William-Souza-Santos/DIGITAL_PID_CONTROL_DCDC_CONVERTER/04 - Text/MATLAB_4SBBC_2.pdf

### 1. Configuração básica de um conversor Buck-Boost

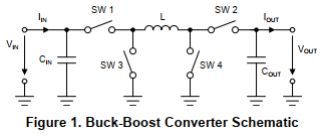
[picture p117: figure]

### 2. Princípio de operação

D̅ = 1 − D

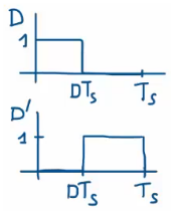
[picture p118: figure]

### 2.1 Buck síncrono

D =

Vo
Vi

Vi > Vo
Apenas duas chaves são comutadas;
Não é possível operar com Vi = Vo or D = 1;
Q3 é totalmente ligado e Q4 é totalmente desligado. Q1 e Q2 são controlados por D e 1 - D, respectivamente, e o conversor se torna um conversor buck sincronizado, conforme mostrado na Figura 4.


### 2.2 Boost síncrono

D = 1 −

Vi
Vo
Apenas duas chaves são comutadas;
Não é possível operar com Vi = Vo or D = 0.
Q1 é totalmente ligado e Q2 é totalmente desligado. Q4 e Q3 são controlados por D e 1 - D, respectivamente, e o conversor se torna um conversor boost sincronizado, conforme mostrado na Figura 5.

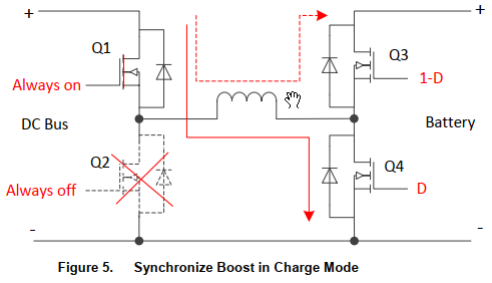
[picture p119: figure]

### 2.3 Buck-Boost síncrono

D =

Vo
Vi + Vo

Vi ≈ Vo
Four switches commutate;
Não é possível operar com Vi = Vo or D = 0.5; Maiores perdas de comutação;
Menor eficiência;
Q1 e Q4 são controlados por D, Q2 e Q3 são controlados por 1-D. O conversor se torna um conversor buck-boost sincronizado, conforme mostrado na Figura 6.

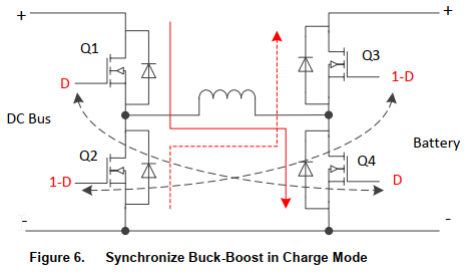
[picture p120: figure]

### 3. Modo de operação

Os quatro interruptores alteram o modo de operação de acordo com a tensão de entrada e a tensão de saída, conforme mostrado na Figura 10. Para evitar um salto entre as operações, uma histerese é adicionada entre a transição do modo buck e buck-boost e entre o modo buck-boost e boost.

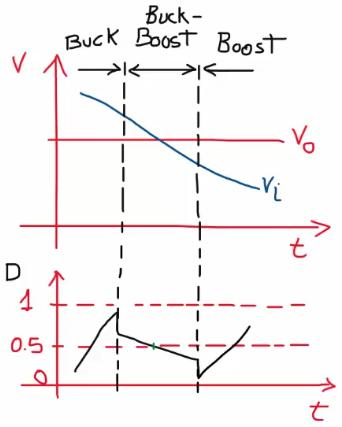
[picture p121: figure]
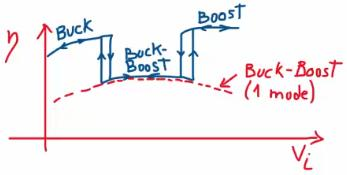
[picture p122: figure]

Um compensador deve ser projetado para operação estável; Há perturbações transitórias durante mudanças de modo.

### 4. Implementação

MOSFETs usados como interruptores;
Os switches superiores (S1, S3) precisam ser acionados;
O tempo de inatividade deve ser adicionado para evitar a corrente de disparo;

Um Bootstrap não pode ser usado: ele não consegue manter os interruptores do lado alto continuamente ligados;
Soluções típicas: gate drivers baseados em transformador e gate drivers baseados em optoacoplador.

### 4.1 Buck

D =

Vo
Vi

L =

1
fΔiL

∗ (Vo −
Vo

2
Vi

)

C =

ΔiL
8fΔVo

### 4.2 Buck-Boost

D =

Vo
Vo + Vi

L =

1
fΔiL

∗

Vo

1 +

Vo
Vi

C =

Io
fΔVo

∗

Vo
Vo + Vi

### 4.3 Boost

D =

Vo − Vi
Vo

L =

1
fΔiL

∗ (Vi −
Vi

2
Vo

)

C =

Io
fΔVo

∗

Vo − Vi
Vo

### 5. Design example

Faixa de tensão de entrada: Vi = [18,30] V Faixa de ciclo de trabalho: D = [0.2,0.8]

Modo de operação | Ciclo de trabalho
Buck | D =
| 1 Vi Vo
Buck-boost | D =
| 1
| 1 + Vi Vo
Boost | D = 1 − Vi Vo

### 5.1 Região Buck

Primeiro calculamos os valores mínimos e máximos da tensão de saída possíveis nessa região com base no ciclo de trabalho determinado.

0.2 =

1
30

Vomin

→ Vomin = 6 V

0.8 =

1
30

Vomax

→ Vomax = 24 V

Agora calculamos uma relação entrada e saída que limitam essa região.

30
24 <

Vi
Vo

≤

30
6

1.25 <

Vi
Vo

≤ 5

Com o limite esquerdo, calculamos as tensões de saída máximas com base na tensão de entrada que determinam a fronteira com a região Buck-Boost.

1.25 =

18
Vo1

→ Vo1 = 14.4 V

1.25 =

30
Vo2

→ Vo2 = 24 V

### 5.2 Região Boost

Primeiro calculamos os valores mínimos e máximos da tensão de saída possíveis nessa região com base no ciclo de trabalho determinado.

0.2 = 1 −

18

Vomin

→ Vomin = 22.5 V

0.8 = 1 −

30

Vomax

→ Vomax = 150 V

Agora calculamos uma relação entrada e saída que limitam essa região.

30
150 ≤

Vi
Vo

<

18
22.5

0.2 ≤

Vi
Vo

< 0.8

Com o limite direito, calculamos as tensões de saída mínimas com base na tensão de entrada que determinam a fronteira com a região Buck-Boost.

18
Vo1

= 0.8 → Vo1 = 22.5 V

30
Vo2

= 0.8 → Vo2 = 37.5 V

### 5.3 Regiões de operação

Faixa de tensão de saída: Vo = [6,55] V

Modo de operação | Ciclo de trabalho | Região de operação | Tensão de operação
Buck | D =
| 1 Vi Vo | Vi Vo > 1.25 | Vi = [18,30] Vo = [6,24]
Buck-Boost | D =
| 1 1 + Vi Vo | 0.80 ≤ Vi Vo ≤ 1.25 | Vi = [18,30] Vo = [14.4,37.5]
Boost | D = 1 − Vi Vo | Vi Vo
| | < 0.80 | Vi = [18,30] Vo = [22.5,55]

### 5.3.1 Regiões de operação


RegionPlot[
{y/x>1.25,0.8<=y/x<=1.25,y/x<0.8}, {x,6,55},
{y,18,30},
PlotStyle->{Blue,Yellow,Red},
BoundaryStyle->None,
FrameLabel->{"Tensão de Saída","Tensão de Entrada"}, PlotLabel->"Região de Operação",
PlotLegends->{"Buck","Buck-Boost","Boost"}]

Com as regiões limitadas, podemos determinar o valor mínimo e máximo da região de operação, conforme a seguir.

0.2 ≤

Vi
Vo

< 0.8 ∩ 1.25 <

Vi
Vo

≤ 5

0.2 ≤

Vi
Vo

≤ 5

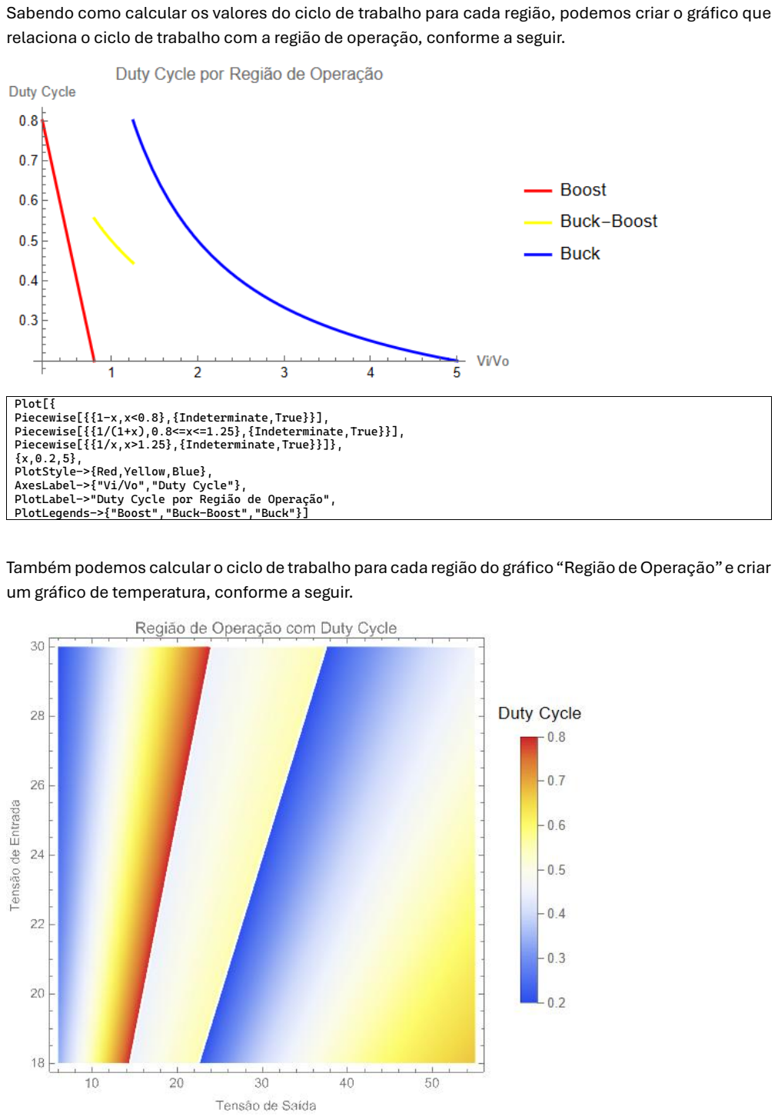
[picture p123: page 10]

Sabendo como calcular os valores do ciclo de trabalho para cada região, podemos criar o gráfico que relaciona o ciclo de trabalho com a região de operação, conforme a seguir.

Plot[{
Piecewise[{{1-x,x<0.8},{Indeterminate,True}}], Piecewise[{{1/(1+x),0.8<=x<=1.25},{Indeterminate,True}}], Piecewise[{{1/x,x>1.25},{Indeterminate,True}}]}, {x,0.2,5},
PlotStyle->{Red,Yellow,Blue},
AxesLabel->{"Vi/Vo","Duty Cycle"}, PlotLabel->"Duty Cycle por Região de Operação",
PlotLegends->{"Boost","Buck-Boost","Buck"}]

Também podemos calcular o ciclo de trabalho para cada região do gráfico “Região de Operação” e criar um gráfico de temperatura, conforme a seguir.

DensityPlot[
Piecewise[{
{x/y,y/x>1.25},
{x/(x+y),0.8<=y/x<=1.25},
{(x-y)/x,y/x<0.8}}],
{x,6,55},
{y,18,30},
ColorFunction->"TemperatureMap", PlotLegends->BarLegend[{"TemperatureMap",{0.2,0.80}}, LegendLabel->"Duty Cycle",
Ticks->Range[0,1,0.1]],
FrameLabel->{"Tensão de Saída","Tensão de Entrada"}, PlotLabel->"Região de Operação com Duty Cycle", RegionFunction->Function[{x,y},6<=x<=55&&18<=y<=30], PlotPoints->64]
Plot3D[
Piecewise[{
{x/y,y/x>1.25},
{x/(x+y),0.80<=y/x<=1.25},
{(x-y)/x,y/x<0.8}}],
{x,6,55},{y,18,30},
AxesLabel->{"Tensão de Saída","Tensão de Entrada","Duty Cycle"}, ColorFunction->Function[{x,y,z},If[y/x>1.25,Blue,If[0.80<=y/x<=1.25,Yellow,Red]]],ColorFunctionScaling->False,BoxRatios->{1,1,1}]

### 5.4 Cálculo dos componentes

Output current: Io = 2 A
Switching frequency: f = 10 kHz Inductor current ripple: 0.6 A (30%)
Output voltage ripple: 1 V (2%)
Modo de operação | Tensão de operação
Buck | Vi = [18,30]
| Vo = [6,24]
Buck-Boost | Vi = [18,30]
| Vo = [14.4,37.5]
Boost | Vi = [18,30]
| Vo = [22.5,55]

### 5.4.1 Buck

Lmax =

1
fΔiL

∗ (Vo −
Vo

2

Vimax

) =
1
10 ∗ 10³ ∗ 0.6

∗ (Vo −
Vo

2
30)

d
dVo

Lmax = 0 → Vo = 15 V

Lmax =

1
10 ∗ 10³ ∗ 0.6

∗ (15 −

15²
30 ) = 1.25 mH

Io=2;
f=10*10^3;
Lr=0.6;
Vr=1;
Lmax[Vi_,Vo_]:=1/(f*Lr)(Vo-Vo^2/Vi); NMaximize[{Lmax[Vi,Vo],18<=Vi<=30,6<=Vo<=24},{Vi,Vo}]
C =

ΔiL
8fΔVo

=

0.6
8 ∗ 10 ∗ 10³ ∗ 1

= 7.5 uF

### 5.2 Buck-Boost

Lmax =

1
fΔiL

∗

Vomax

1 +

Vomax
Vimax

=

1
10 ∗ 10³ ∗ 0.6

∗

37.5

1 +

37.5
30

= 2.78 mH

Cmax =

Io
fΔVo

∗

Vomax

Vomax + Vimin

=

2
10 ∗ 10³ ∗ 1

∗

37.5
37.5 + 18 = 135.1 uF

### 5.3 Boost

Lmax =

1
fΔiL

∗ (Vi −
Vi

2

Vomax

) =
1
10 ∗ 10³ ∗ 0.6

∗ (Vi −
Vi

2
55)

d
dVi

Lmax = 0 → Vi = 27.5 V

Lmax =

1
10 ∗ 10³ ∗ 0.6

∗ (27.5 −
27.5

2
55 ) = 2.29 mH

Io=2;
f=10*10^3;
Lr=0.6;
Vr=1;
Lmax[Vi_,Vo_]:=1/(f*Lr)*(Vi-Vi^2/Vo); NMaximize[{Lmax[Vi,Vo],18<=Vi<=30,22.5<=Vo<=55},{Vi,Vo}]

Cmax =

Io
fΔVo

∗

Vomax − Vimin

Vomax

=

2
10 ∗ 10³ ∗ 1

∗

55 − 18
55 = 134.5 uF

### 5.4 Verification

L = 2.78 mH

C = 135.1 uF

### 5.4.1 Buck

2.78 ∗ 10⁻³ =

1
10 ∗ 10³ ∗ ΔiL

∗ (15 −

15²
30 ) → ΔiL = 0.27 A

135.1 ∗ 10⁻⁶ =

0.27
8 ∗ 10 ∗ 10³ ∗ ΔVo

→ ΔVo = 0.025 V

### 5.4.2 Buck-Boost

2.78 ∗ 10⁻³ =

1
10 ∗ 10³ ∗ ΔiL

∗

37.5

1 +

37.5
30

→ ΔiL = 0.6 A

135.1 ∗ 10⁻⁶ =

2
10 ∗ 10³ ∗ ΔVo

∗

37.5
37.5 + 18

→ ΔVo = 1 V

### 5.4.2 Boost

2.78 ∗ 10⁻³ =

1
10 ∗ 10³ ∗ ΔiL

∗ (27.5 −
27.5

2
55 ) → ΔiL = 0.49 A

135.1 ∗ 10⁻⁶ =

2
10 ∗ 10³ ∗ ΔVo

∗

55 − 18
55

→ ΔVo = 1 V

Modo de
operação

Faixa de
operação (V) | Duty Cycle | Vi/Vo | ΔiLmax
| | | (A)

ΔVomax
(V)
Buck | Vi = [18,30]
Vo = [6,24] | D = [0.2,0.8] | 0.2 ≤ Vi
| | Vo
< 0.8 | 0.27 | 0.025

Buck-Boost

Vi = [18,30] Vo = [14.4,37.5] | D = [0. 4̅, 0. 5̅] | 0.8 ≤ Vi
| | Vo
≤ 1.25 | 0.6 | 1
Boost | Vi = [18,30]
Vo = [22.5,55] | D = [0.2,0.8] | 1.25 < Vi
| | Vo
≤ 5 | 0.49 | 1

### 5.5 Simulink implementation

O circuito base do conversor é implementado no Simulink em um subsistema conforme abaixo.

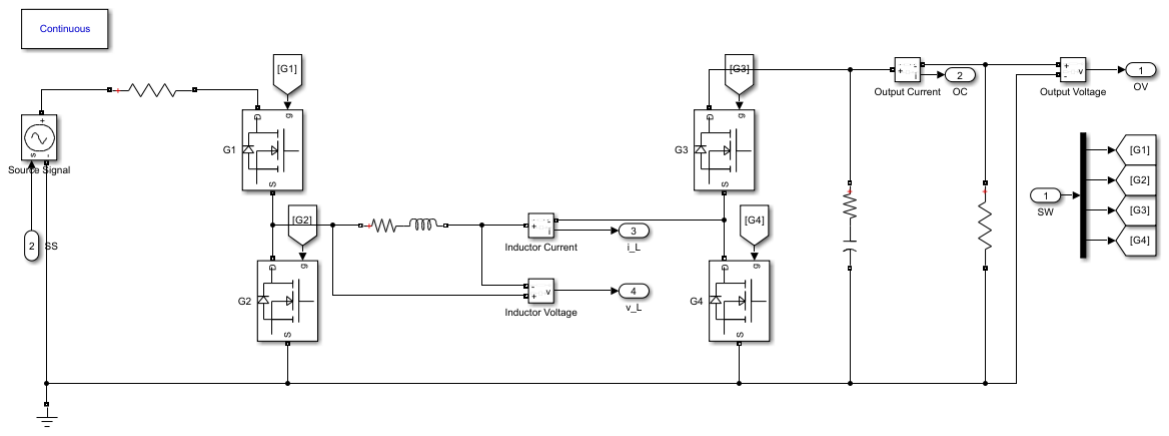
[picture p124: figure]

O subsistema possui 2 entradas, sendo elas: Source Signal (SS) e SW ( 4 Switches multiplexados). E 4 saídas, sendo elas: Output Voltage (OV), Output Current (OC), Inductor Voltage (v_L) e Inductor Current (i_L).
Os 4 modos de funcionamento dependem do estado dos 4 Switches e do seu Duty Cycle respectivo. Como temos 4 modos diferentes, precisamos de 2 bits para representar os modos. A tabela abaixo resume a lógica da ativação de cada Switch usando A e B como entradas lógicas.
Mode | AB | SW1 | SW2 | SW3 | SW4
Buck | 00 | D | 1 - D | 1 | 0
Buck-boost | 01 | D | 1 - D | 1 - D | D
Boost | 11 | 1 | 0 | 1 - D | D
Off | 10 | 0 | 0 | 0 | 0

Usando conhecimentos de sistemas digitais, podemos simplificar a relação para cada Switch, chegando nas equações abaixo.

SW1 = A̅D + AB

SW2 = A̅D̅

SW3 = A̅B̅ + BD̅

SW4 = BD

A partir das relações acima, podemos implementar no Simulink um subsistema para aplicar o funcionamento de cada Switch a partir das entradas A, B e D.


O modo de funcionamento atual e futuro do sistema é definido a partir da relação entre Tensão de Entrada e Tensão de Referência, conforme a tabela abaixo.

Modo de operação | Vi/Vo
Buck | 1.25 <

Vi
Vo

≤ 5

Buck-Boost 0.8 ≤

Vi
Vo

≤ 1.25

Boost | 0.2 ≤

Vi
Vo

< 0.8

A tabela indica que, enquanto a Tensão de Entrada estiver acima de 125% da Tensão de Referência, o modo de funcionamento será Buck. E, enquanto a Tensão de Entrada estiver abaixo de 80% da Tensão de Referência, o modo de funcionamento será Boost.
Podemos escrever essa relação conforme abaixo.

X =

Vi
Vo

> 1.25

Y =

Vi
Vo

> 0.8

A tabela abaixo resume a lógica do modo de funcionamento acima.

XY | Buck | Buck-Boost | Boost
00 | 0 | 0 | 1
01 | 0 | 1 | 0
11 | 1 | 0 | 0
10 | X | X | X

Usando conhecimentos de sistemas digitais, podemos simplificar a relação, chegando nas equações abaixo.

Buck = X

Buck-Boost = X̅Y

Boost = Y̅
A lógica acima pode ser implementada no Simulink usando o subsistema a seguir.

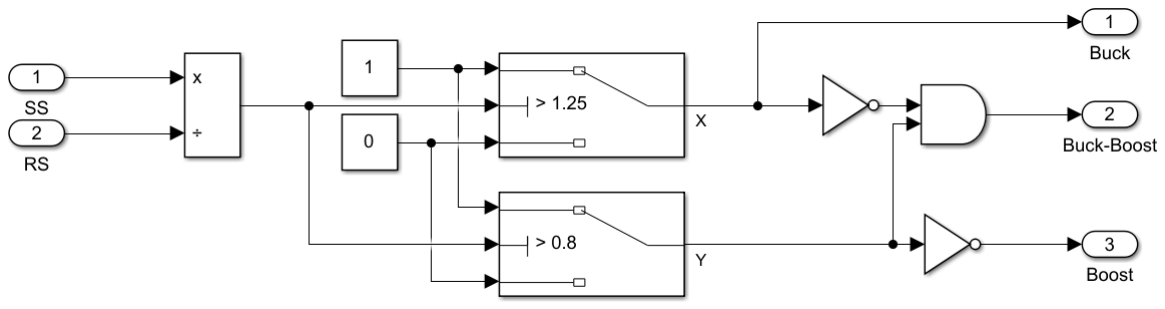
[picture p125: figure]

Agora que temos definido qual modo será ativado, precisamos do cálculo do Duty Cycle. Cada modo terá seu Duty Cycle calculado, porém somente aquele ativado no momento será usado no funcionamento dos Switches. Conforme vimos anteriormente, para o cálculo precisamos somente da Tensão de Entrada e Tensão de Referência, conforme a seguir.


O valor de A e B, escolhido anteriormente conforme a tabela abaixo, também é anexado junto ao seu respectivo D pelo MUX.

Mode | AB
Buck | 00
Buck-boost | 01
Boost | 11

Para definir qual valor será utilizado, usamos o resultado do subsistema anterior juntamente com comparadores lógicos para levar o valor até as variáveis A, B e D pelo DEMUX, conforme abaixo.

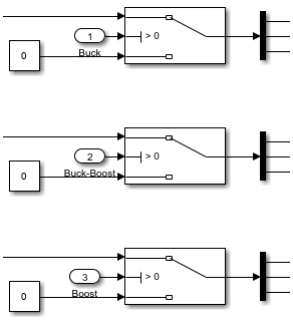
[picture p126: figure]

Como somente um dos comparadores estará ativo por vez, A e B pode ser calculado com uma porta OR enquanto D pode ser calculado como uma soma simples, conforme abaixo.

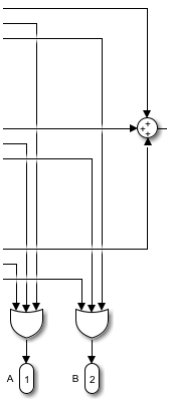
[picture p127: figure]

Por fim, para propósitos de controle, podemos somar a variável D com uma entrada externa (D_FIS). Também, como definido anteriormente, o Duty Cycle é saturado entre 0.2 e 0.8.

Assim, obtemos nosso subsistema responsável por determinar a variável D do sistema.


Com as variáveis A, B e D determinadas, o funcionamento dos Switches também estão determinados e, portanto, o sistema está pronto para funcionamento em malha aberta.
Para visualizar o erro e sua variação precisamos de um subsistema. O erro pode ser definido pelo quão distante está a Tensão de Saída da Tensão de Referência e a variação do erro pode ser definida pela diferença entre o erro atual e anterior, assumindo o uso de valores discretos. Para facilitar a visualização do desempenho, vamos empregar um erro normalizado, conforme abaixo.

E[n] =

Vo − Vr
|Vo − Vr

| + 1

dE[n] = E[n] − E[n − 1]

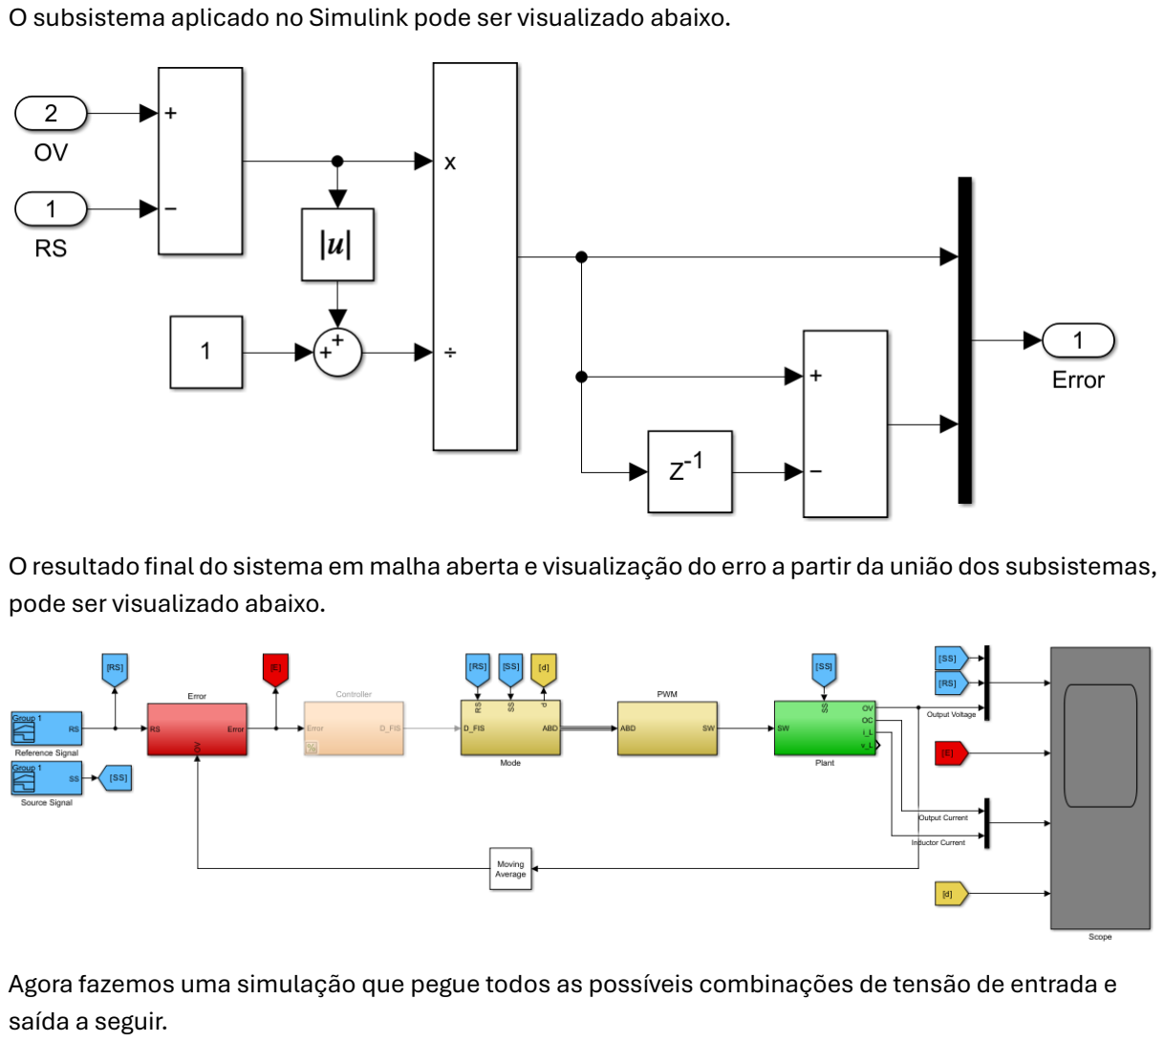
[picture p128: page 19]

O subsistema aplicado no Simulink pode ser visualizado abaixo.

O resultado final do sistema em malha aberta e visualização do erro a partir da união dos subsistemas, pode ser visualizado abaixo.

Agora fazemos uma simulação que pegue todos as possíveis combinações de tensão de entrada e saída a seguir.

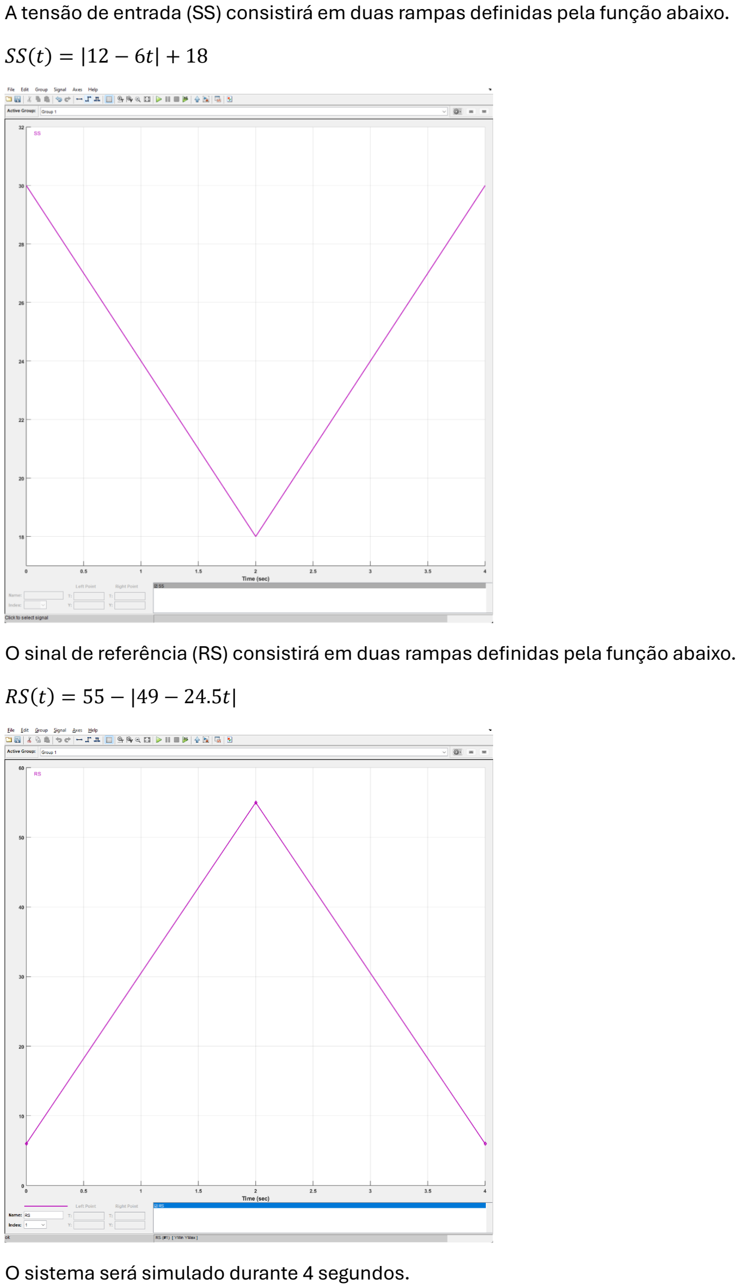
[picture p129: page 20]

A tensão de entrada (SS) consistirá em duas rampas definidas pela função abaixo.

SS(t) = |12 − 6t| + 18

O sinal de referência (RS) consistirá em duas rampas definidas pela função abaixo.

RS(t) = 55 − |49 − 24.5t|

O sistema será simulado durante 4 segundos.


Podemos identificar facilmente os pontos de transição do modo de operação pela falta de histerese. Também se observa um erro na tensão de saída (vermelho) pela falta de um compensador.


Nota-se uma taxa de variação inicial do erro (magenta) por causa da ativação do sistema até sua operação em estado estacionário, e outras variações durante a troca de operação. O erro (vermelho) indica que o sistema não atinge e fica abaixo da tensão de referência durante seu funcionamento pela falta de um compensador.

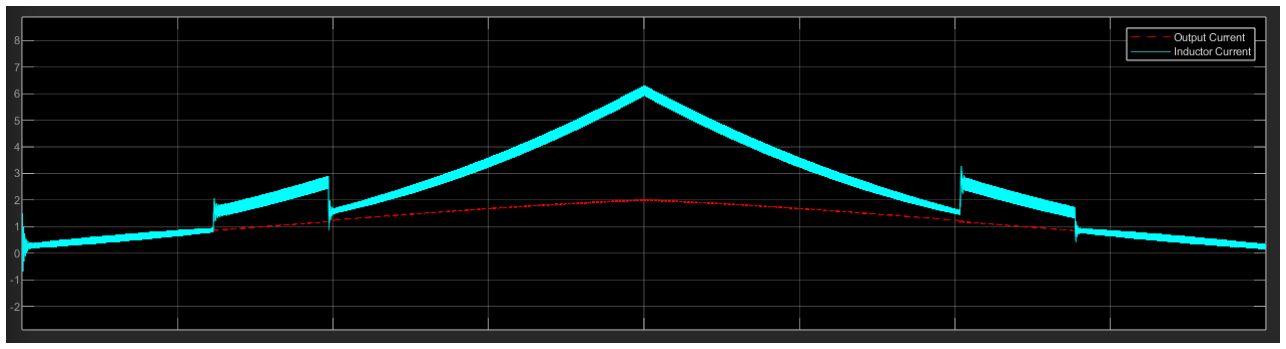
[picture p130: figure]

A corrente do indutor ficou abaixo de 6 A, não levando em consideração o ripple de 0.6 A. A corrente de saída permaneceu abaixo 2 A.


O valor do Duty Cycle obedece ao cálculo do modo de operação e se mantém no range designado anteriormente de 0.2 a 0.8. O valor do controle segue os mesmos valores pois não há um compensador implementado.

### 5.5.1 Controle

Usaremos um Fuzzy Inference System (FIS) como compensador e corrigir o erro do sistema. Sabemos que o comportamento do sistema depende do Duty Cycle, então iremos compensar esse valor e usá-la como variável manipulada.
A partir do subsistema de erro, temos que ele varia entre -1 e 1. Um erro negativo indica que a Tensão de Saída (variável controlada) está abaixo da Tensão de Referência e precisamos de uma compensação positiva no Duty Cycle, enquanto um erro positivo indica estar acima e precisamos de uma compensação negativa.
Com as informações anteriores, podemos criar um FIS com uma entrada, denominada Error, e uma saída, denominada Mode. Para determinar os pesos das entradas usaremos uma função membro em formato Z para erros negativos e uma função membro em formato S para erros positivos, conforme a abaixo.


Para determinar o ajuste na saída, usaremos uma função membro em formato de sino para saídas negativas e saídas positivas, conforme abaixo.


Com isso, obtemos uma superfície que descreve o comportamento do FIS.


Observando o gráfico acima, percebemos que erros próximos de 0 terão poucos ajustes, enquanto erros próximos de -0.5 e 0.5 terão seus ajustes máximos. Isso reflete o erro normalizado, que cresce muito quando se afaste de 0.

Agora criaremos uma tabela verdade que irá servir de consulta para determinar a saída com base na superfície anterior, a tabela verdade terá 32 pontos.


Com isso podemos criar o subsistema de controle que aplica a tabela verdade para compensar o Duty Cycle no sistema, conforme a seguir.

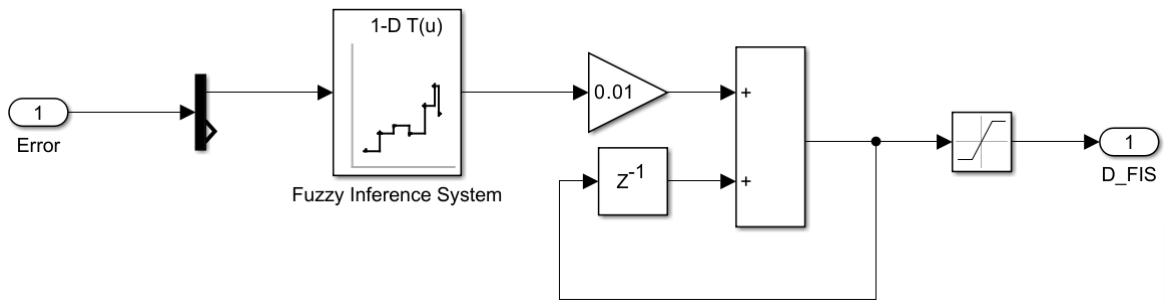
[picture p131: figure]

Para evitar ajustes instantâneos no sistema e instabilidade, adicionamos um integrador discreto que leva até o ponto de ajuste de forma suave. Também um saturador é utilizado para evitar acúmulo de esforço no integrador.

Por fim, temos o sistema completo no Simulink, conforme abaixo.

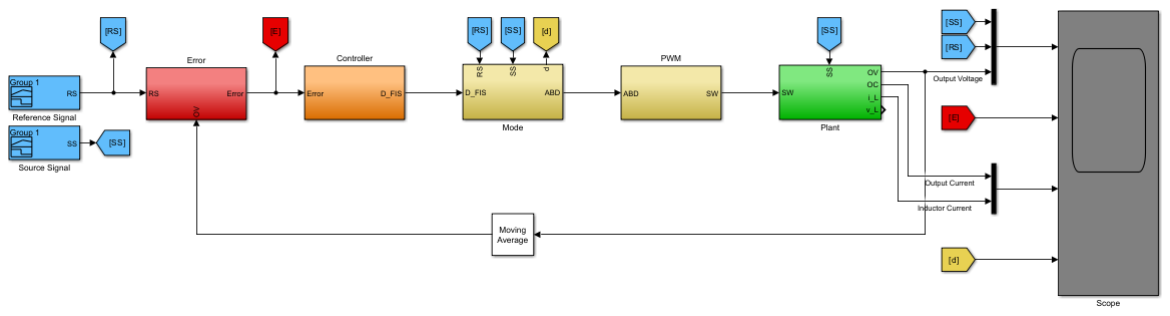
[picture p132: figure]

A simulação seguirá as mesmas condições anteriores, porém com a adição do controlador.


Podemos identificar facilmente os pontos de transição do modo de operação pela falta de histerese. Também se observa que a saída acompanhou a tensão de referência.

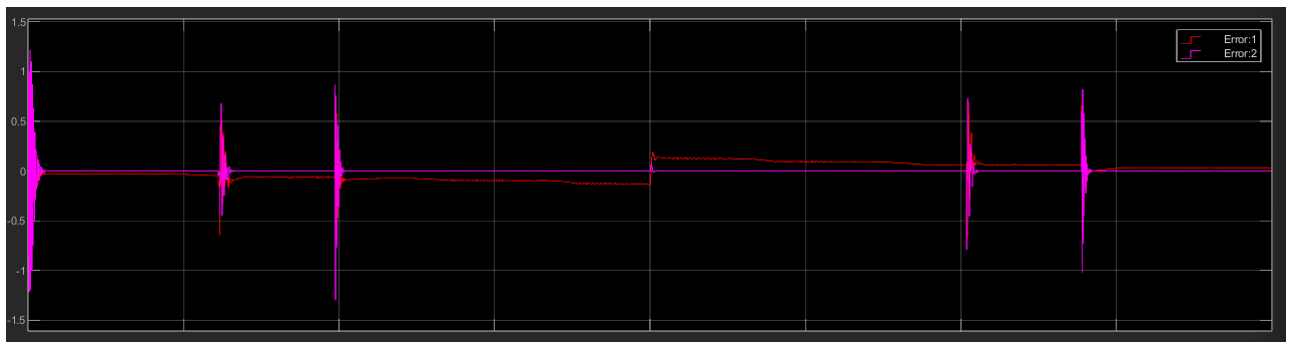
[picture p133: figure]

Nota-se uma taxa de variação inicial do erro (magenta) por causa da ativação do sistema até sua operação em estado estacionário, e outras variações durante a troca de operação. O erro (vermelho) indica que a saída do sistema fica próximo da tensão de referência, porém não exatamente 0, considerando o uso de um erro normalizado.

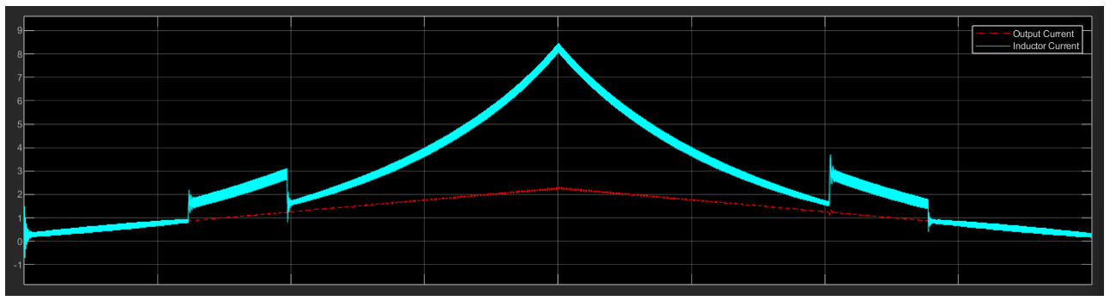
[picture p134: figure]

A corrente do indutor ficou abaixo de 8 A, não levando em consideração o ripple de 0.6 A. A corrente de saída permaneceu abaixo 2 A. Ou seja, pela ação do compensador houve um aumento na corrente de entrada.


O valor do Duty Cycle obedece ao cálculo do modo de operação e se mantém no range designado anteriormente de 0.2 a 0.8. O valor do controlado foi compensado, principalmente na parte com modo de operação Buck-Boost.
Com isso observamos que para realizar a correção houve um aumento na corrente de entrada, que deverá ser levado em conta no projeto.
