William-Souza-Santos/DIGITAL_PID_CONTROL_DCDC_CONVERTER/04 - Text/Fonte/buck_boost_formulas.pdf

## Dimensionamento de um Conversor DC-DC Buck-Boost Bidirecional

1. Razão Cíclica (Duty Cycle)
- Modo Buck (Step-Down):
D = V_out / V_in
Onde:
- D = razão cíclica
- V_out = tensão de saída
- V_in = tensão de entrada
- Modo Boost (Step-Up):
D = 1 - (V_in / V_out)
- Modo Buck-Boost:
D = V_out / (V_out + V_in)
2. Indutor
- Corrente Média no Indutor:
I_L = P_out / V_out
Onde:
- I_L = corrente média no indutor
- P_out = potência de saída
- Indutância Mínima:
L_min = (1-D)D V_in / (f_s * DeltaI_L) Onde:
- L_min = indutância mínima necessária
- f_s = frequência de chaveamento
- DeltaI_L = ripple de corrente do indutor (10-40% de I_L)

3. Capacitância de Saída
- Para limitar o ripple de tensão na saída: C_out = (I_L * D) / (f_s * DeltaV_out) Onde:
- C_out = capacitância de saída necessária
- DeltaV_out = ripple de tensão desejado
4. Capacitância de Entrada
- Para estabilizar a tensão de entrada:
C_in = (I_L * (1-D)) / (f_s * DeltaV_in)
Onde:
- C_in = capacitância de entrada necessária
- DeltaV_in = ripple de tensão na entrada
5. Carga Mínima para Operar no Modo de Condução Contínua (MCC)

A condição para operar no modo contínuo é:

I_L,min = I_out * (1-D) > (DeltaI_L / 2)

Podemos expressar a corrente de carga mínima como:

R_load,min = V_out / I_out,min

Onde:
- R_load,min = resistência mínima de carga para modo contínuo
- I_out,min = corrente mínima de saída

I_out,min = (D * V_in) / (2 * f_s * L)

A carga mínima que garante operação contínua é:

R_load,min = (2 * f_s * L * V_out) / (D * V_in)

6. Carga Máxima do Conversor

A corrente de saída máxima pode ser aproximada por:

I_out,max = I_L,max / (1-D)

Onde:
- I_out,max = corrente máxima de saída
- I_L,max = corrente máxima no indutor

E a carga máxima é:

R_load,max = V_out / I_out,max = (V_out * (1-D)) / I_L,max

Onde:
- R_load,max = resistência máxima de carga que o conversor suporta.
