William-Souza-Santos/DIGITAL_PID_CONTROL_DCDC_CONVERTER/03 - Hadware/06 - 3D View/DC_DC_CONVERTER_TOP2.jpg

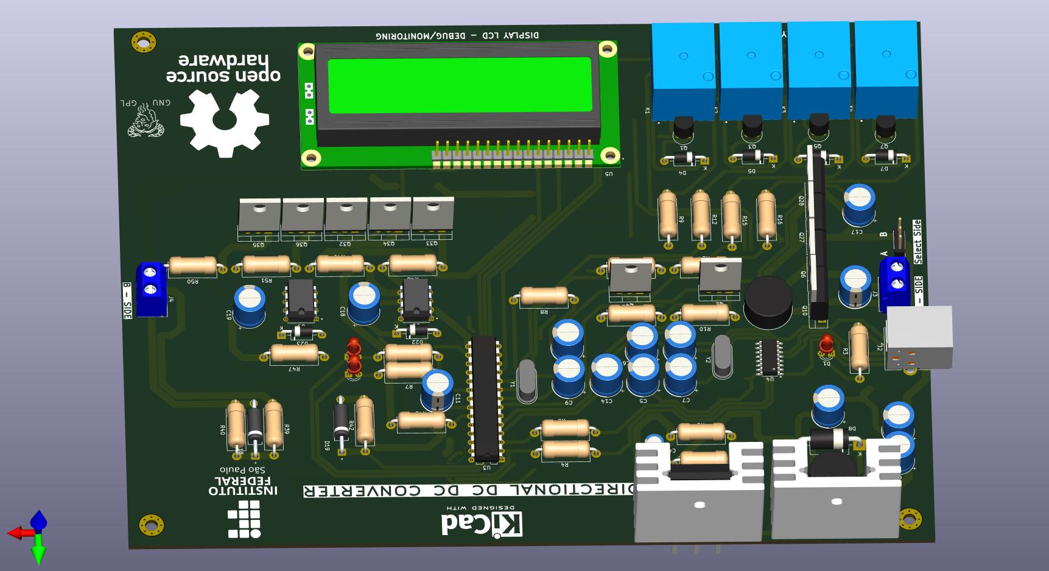
03 - Hadware/06 - 3D View/DC_DC_CONVERTER_TOP2.jpg
