William-Souza-Santos/DIGITAL_PID_CONTROL_DCDC_CONVERTER/03 - Hadware/06 - 3D View/Figura3D_2.jpg

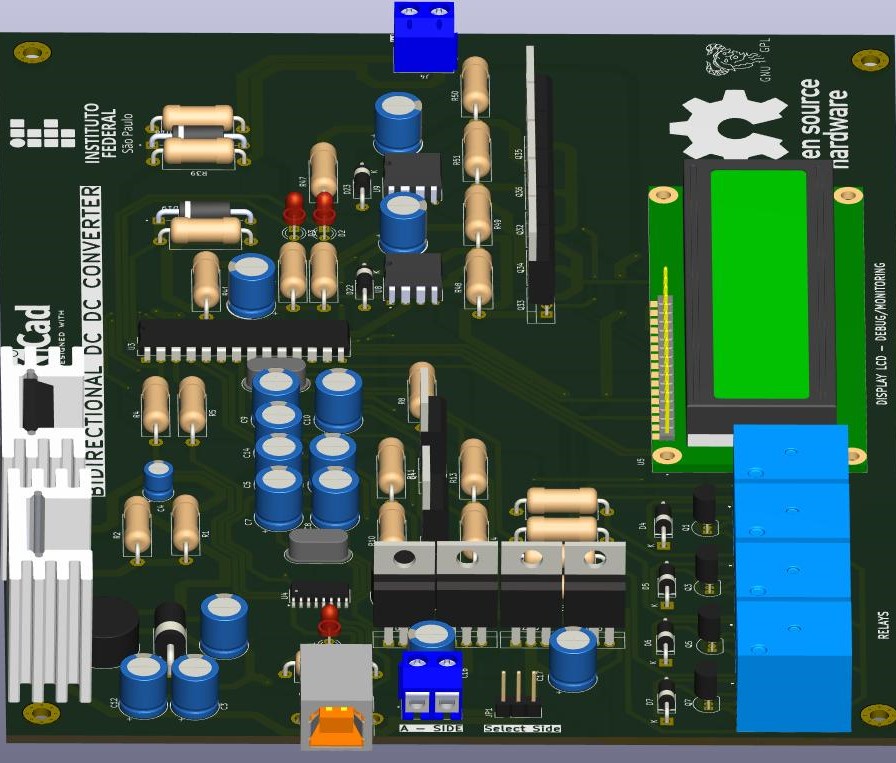
03 - Hadware/06 - 3D View/Figura3D_2.jpg
