William-Souza-Santos/DIGITAL_PID_CONTROL_DCDC_CONVERTER/03 - Hadware/06 - 3D View/Proteus.png

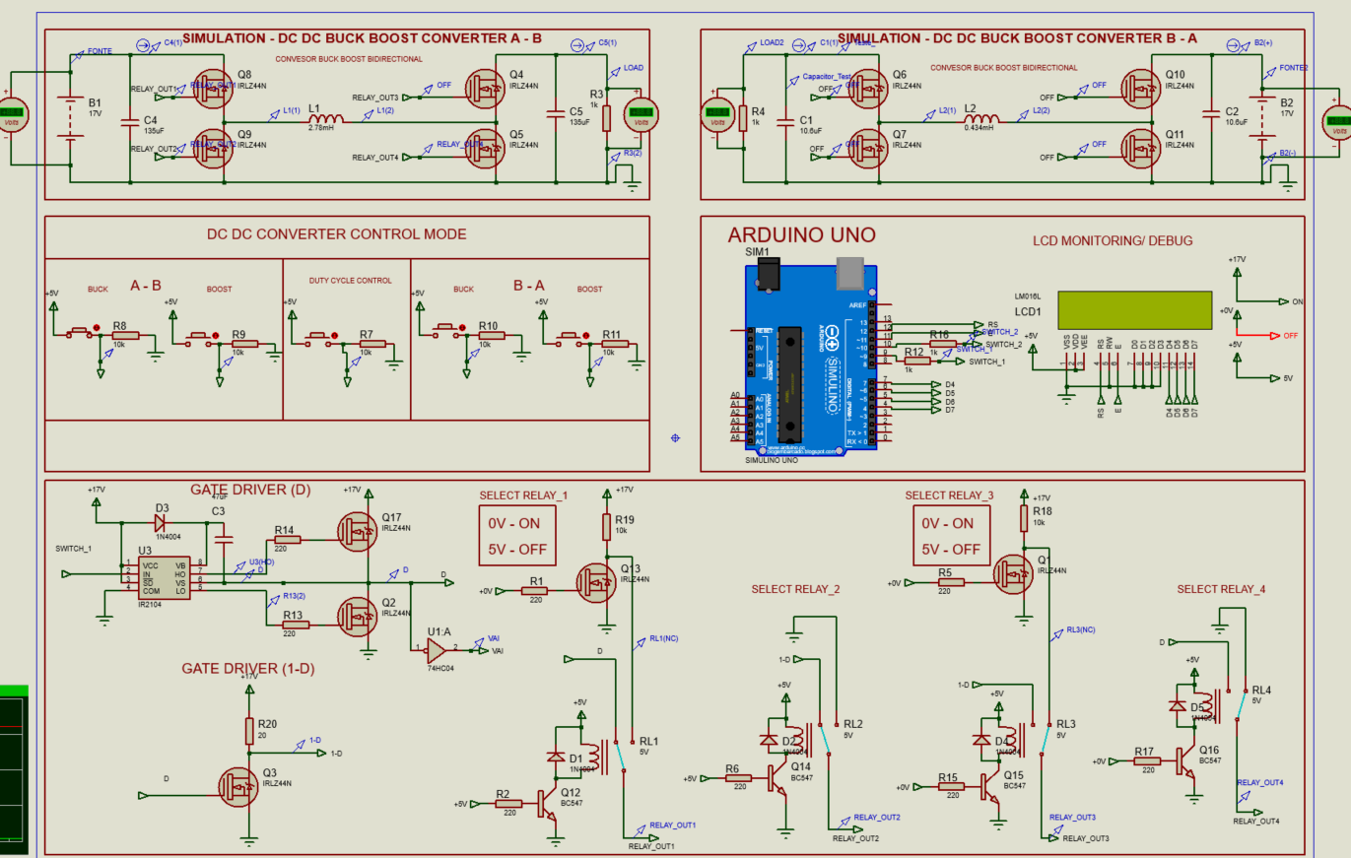
03 - Hadware/06 - 3D View/Proteus.png
