William-Souza-Santos/DIGITAL_PID_CONTROL_DCDC_CONVERTER/06 - Proteus Simulation/Modo_Texas.png

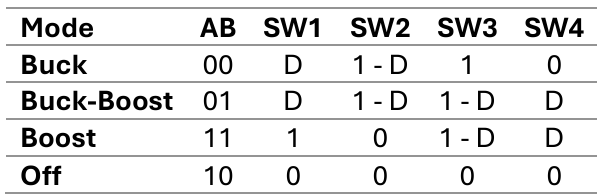
06 - Proteus Simulation/Modo_Texas.png
