William-Souza-Santos/DIGITAL_PID_CONTROL_DCDC_CONVERTER/06 - Proteus Simulation/Modos.bmp

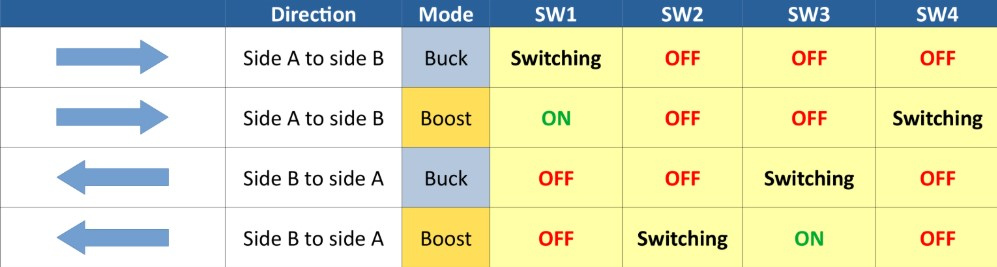
06 - Proteus Simulation/Modos.bmp
