William-Souza-Santos/DIGITAL_PID_CONTROL_DCDC_CONVERTER/09 - Pictures/Curves_Boost.bmp

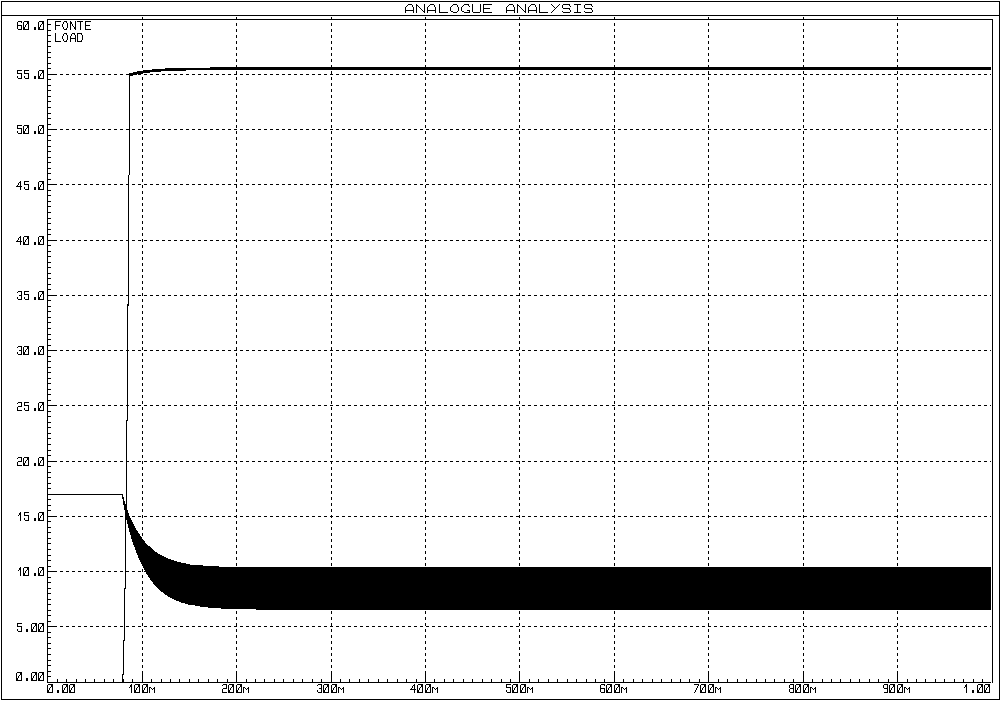
09 - Pictures/Curves_Boost.bmp
