William-Souza-Santos/DIGITAL_PID_CONTROL_DCDC_CONVERTER/09 - Pictures/Gate_Driver.png

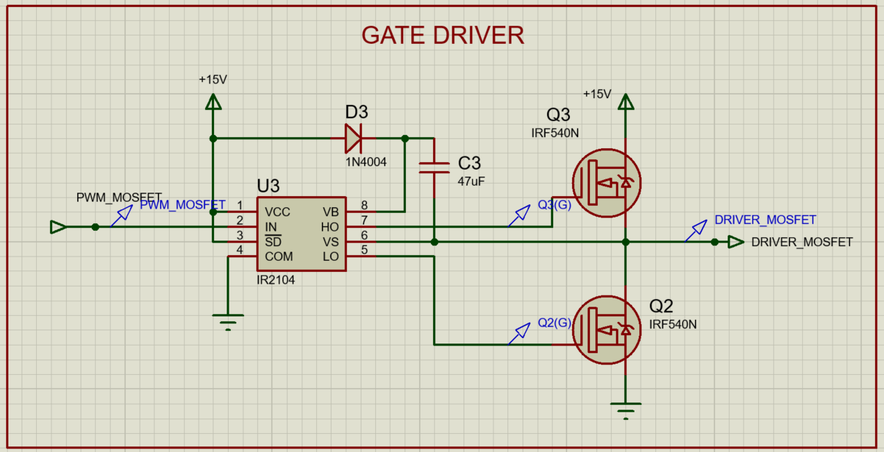
09 - Pictures/Gate_Driver.png
