William-Souza-Santos/DIGITAL_PID_CONTROL_DCDC_CONVERTER/03 - Hadware/02 - Layout/Layout Final Version.pdf

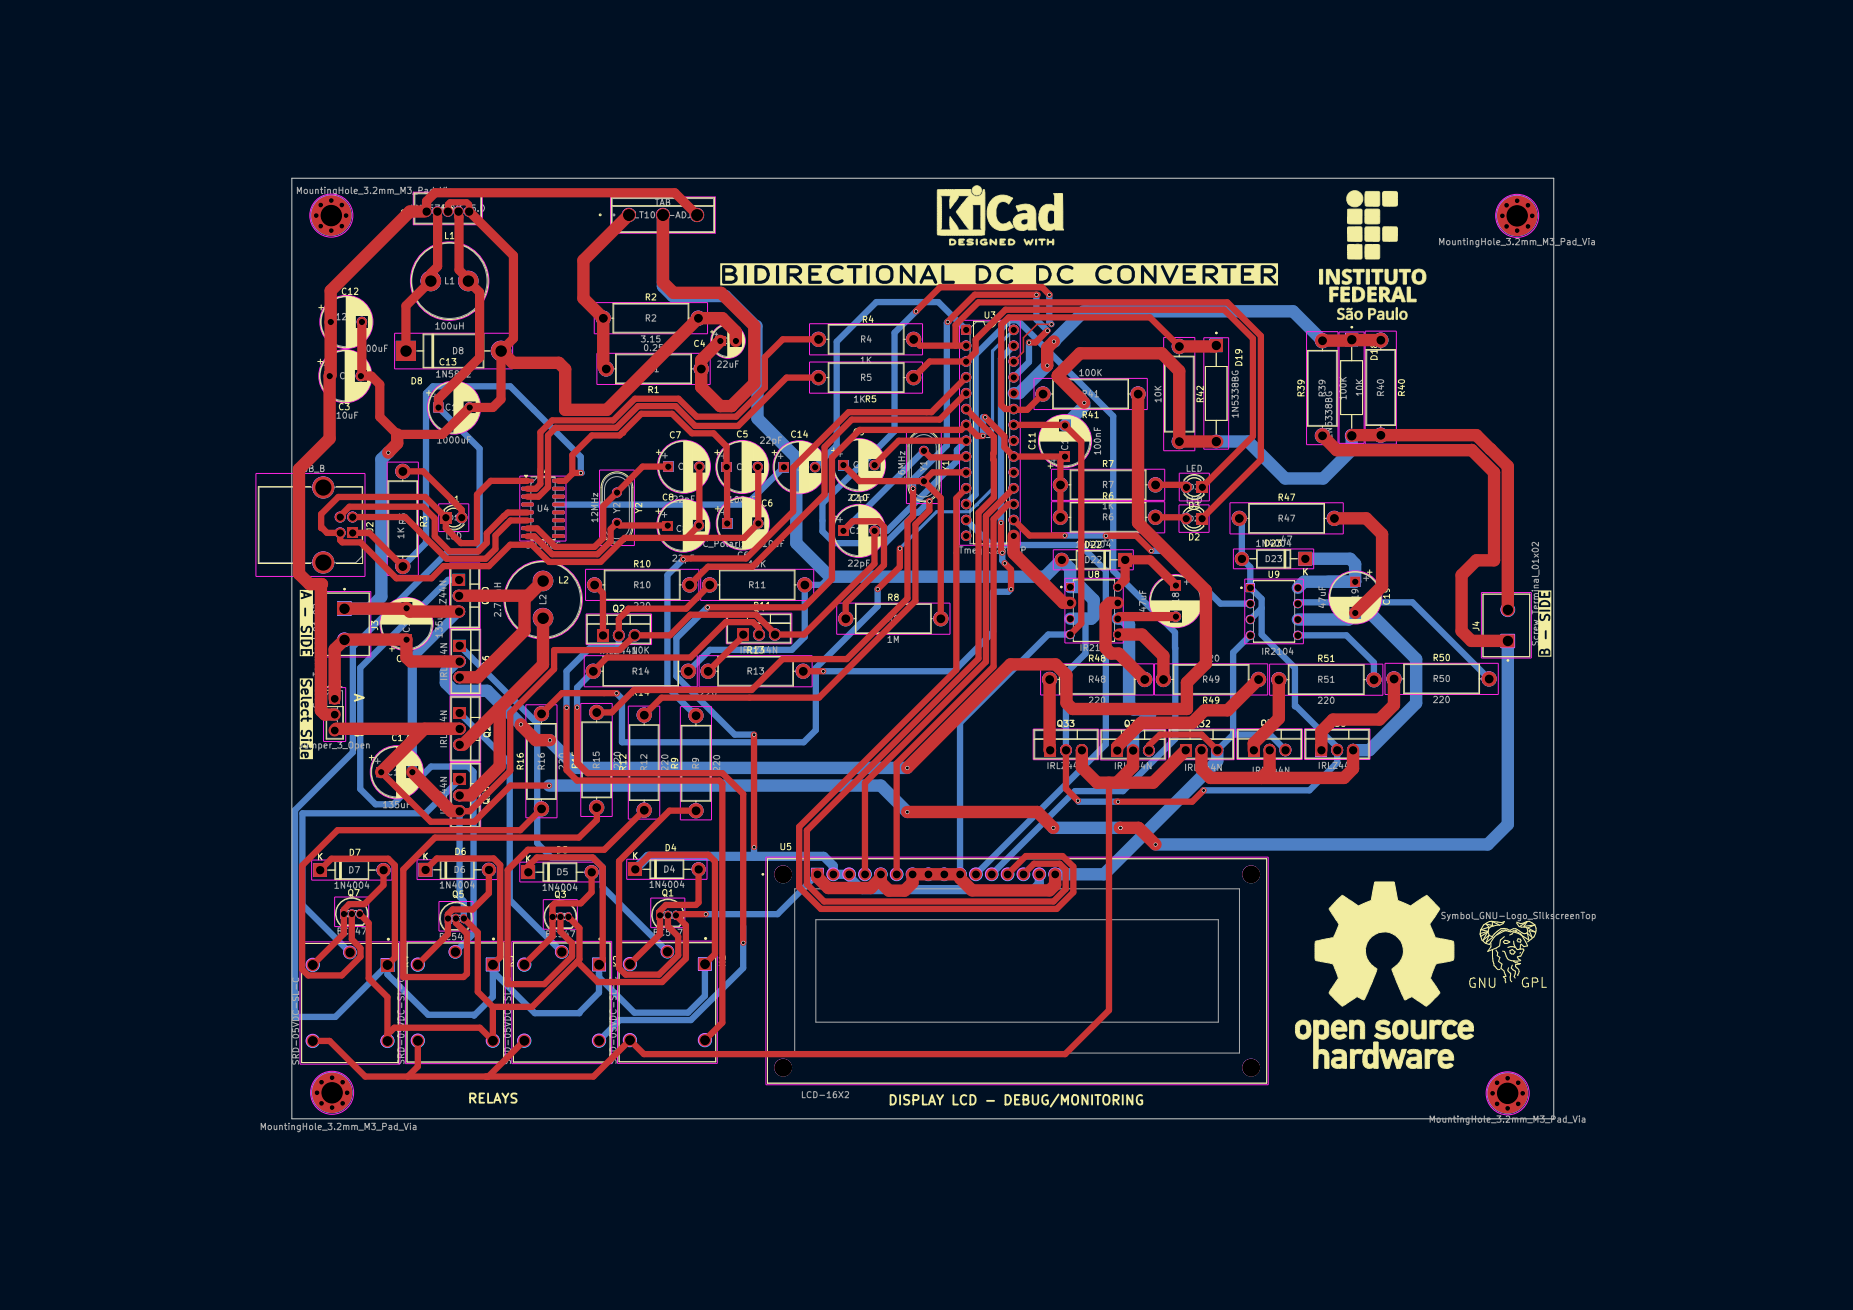
[picture p197: page 1]
