William-Souza-Santos/DIGITAL_PID_CONTROL_DCDC_CONVERTER/03 - Hadware/02 - Layout/Layout Final Version (2).pdf

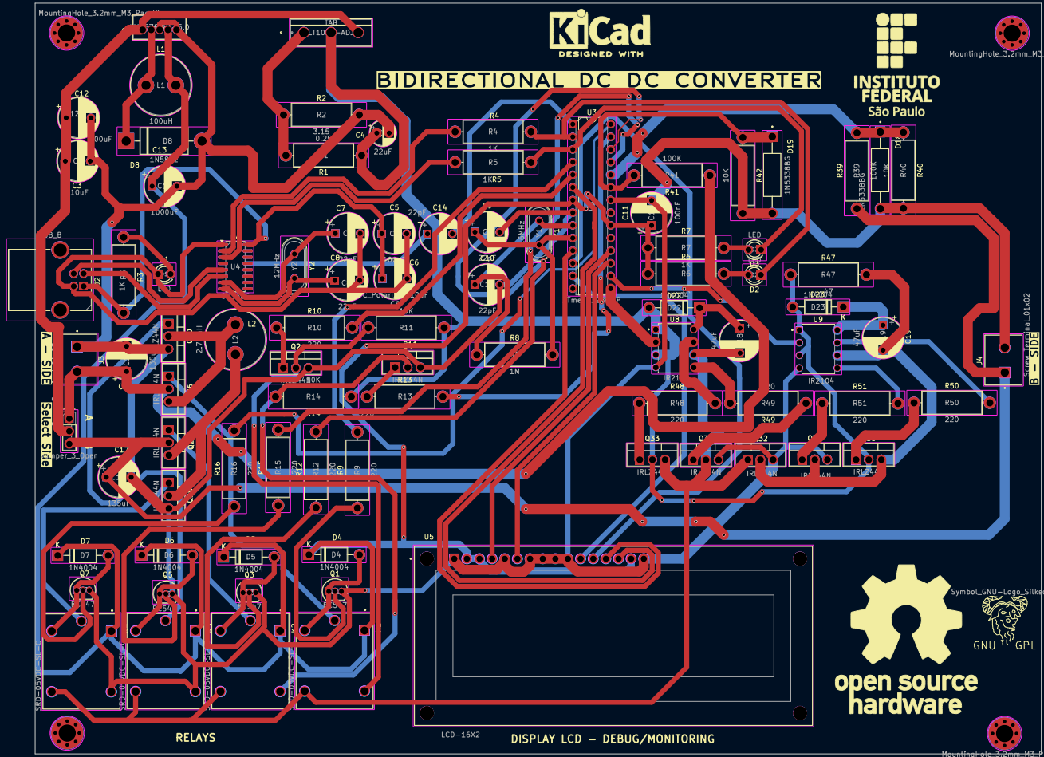
[picture p198: page 1]
