William-Souza-Santos/DIGITAL_PID_CONTROL_DCDC_CONVERTER/07 - LTSPICE Simulation/DC_DC_Converter.asc

C1: cap; 100µ
D1: diode; IdealDiode
L1: ind; 348µ
R1: res; 12
S1: sw
V1: voltage; 9
V2: voltage; PULSE(0 1 0 1n 1n {Dmax/Fs} {1/Fs})
Named nets: 0
.tran 0 0.0202 0.02
.model SW SW(Ron=1n Roff=1000Meg Vt=0.0001)
.model IdealDiode D(Ron=1n Roff=100Meg Vfwd = 0.0001 Vrev=1000)
.param Fs=50k Dmin=0.4615 Dmax=0.5714
DC DC CONVERTER BUCK BOOST EXEMPLO
