William-Souza-Santos/DIGITAL_PID_CONTROL_DCDC_CONVERTER/02 - Software/01 - Firmware/Protheus_Simulation_Firmware/Protheus_Simulation_Firmware.ino

/*
  Blink

  Turns an LED on for one second, then off for one second, repeatedly.

  Most Arduinos have an on-board LED you can control. On the UNO, MEGA and ZERO
  it is attached to digital pin 13, on MKR1000 on pin 6. LED_BUILTIN is set to
  the correct LED pin independent of which board is used.
  If you want to know what pin the on-board LED is connected to on your Arduino
  model, check the Technical Specs of your board at:
  https://www.arduino.cc/en/Main/Products

  modified 8 May 2014
  by Scott Fitzgerald
  modified 2 Sep 2016
  by Arturo Guadalupi
  modified 8 Sep 2016
  by Colby Newman

  This example code is in the public domain.

  https://www.arduino.cc/en/Tutorial/BuiltInExamples/Blink
*/




#include <LiquidCrystal.h>

LiquidCrystal lcd(12, 11, 7, 6, 5, 4);

const int pwmPin = 9; // Pino para o PWM (OC1A)
float DUTY_CYCLE = 0;

bool usarComplementar = true; // false = PWM normal, true = PWM complementar (invertido)

void setup() {
  pinMode(LED_BUILTIN, OUTPUT);
  pinMode(pwmPin, OUTPUT);

  // Configura o Timer1 para gerar PWM de 10 kHz
  TCCR1A = 0;
  TCCR1B = 0;
  TCNT1 = 0;

  ICR1 = 1600; // TOP = 1600 → 16MHz / 1600 = 10kHz
  OCR1A = 1200; // 50% de duty cycle

 DUTY_CYCLE = (int)(((float)OCR1A / ICR1) * 100); // Cálculo correto do duty cycle

  if (!usarComplementar) {
    TCCR1A = (1 << COM1A1) |            // OC1A normal (não-invertido)
             (1 << WGM11);              // Modo PWM rápido com ICR1 como TOP
  } else {
    TCCR1A = (1 << COM1A1) | (1 << COM1A0) | // OC1A invertido (complementar)
             (1 << WGM11);
  }

  TCCR1B = (1 << WGM13) | (1 << WGM12) | (1 << CS10); // Prescaler = 1, modo PWM rápido

  //DUTY_CYCLE = ((float)OCR1A / ICR1) * 100;

lcd.begin(16, 2);
  lcd.print("DC DC CONVERTER");
  lcd.setCursor(2, 1);
  lcd.print("BUCK BOOST");  
  //delay(500); // Exibe a mensagem por 500 ms antes de limpar
  lcd.clear();
}

void loop() {
  lcd.setCursor(0, 0);
  lcd.print("DUTY CYCLE: ");
  lcd.print(DUTY_CYCLE, 1); // Exibe com uma casa decimal
  lcd.print("%  ");

  digitalWrite(LED_BUILTIN, HIGH);
  delay(1);
  digitalWrite(LED_BUILTIN, LOW);
  delay(1);
}
